NANOmodules/NANO-Minipops/CODE/NANO-Minipops/Includes.h

// All in the spirit of open-source and open-hardware
//
// Minipops rhythm box (c) DSP Synthesizers 2016
// Code by Jan Ostman
// 
// Design by Jorge Gutiérrez
// 
// 2018 Spain
//
// Free for non commercial use
//
// NANO Modules
//
// O2 Minipops rhythm box (c) DSP Synthesizers 2016
// Free for non commercial use

// http://janostman.wordpress.com


// The value will quickly become too large for an int to store
unsigned long previousMicros = 0; 
unsigned long currentMicros = 0;

//--------- Ringbuf parameters ----------
uint8_t Ringbuffer[256];
uint8_t RingWrite=0;
uint8_t RingRead=0;
uint8_t activeRead=5;
volatile uint8_t RingCount=0;
volatile uint16_t SFREQ;
//-----------------------------------------

//Patterns GU BG2 BD CL CW MA CY QU
/*
16 steps
------------
Hard rock
Disco
Reggae
Rock
Samba
Rumba
Cha-Cha
Swing
Bossa Nova
Beguine
Synthpop
12-steps
---------
Boogie
Waltz
Jazz rock
Slow rock
Oxygen
 */

const unsigned char patlen[16] PROGMEM = {15,15,15,15,15,15,15,15,15,15,15,11,11,11,11,11};

const unsigned char pattern[256] PROGMEM = {
B00101100,      //Hard rock16
B00000000,
B00000100,
B00000000,
B00101110,
B00000000,
B00100100,
B00000000,
B00101100,
B00000000,
B00000100,
B00000000,
B00101110,
B00000000,
B00000100,
B00000000,

B00100100,      //Disco16
B00000000,
B00000100,
B00010100,
B00100110,
B00000000,
B00000001,
B00000100,
B00100100,
B00000000,
B00000100,
B00000100,
B01100110,
B00000100,
B01000001,
B00000000,

B01000001,      //Reegae16
B00000100,
B10000000,
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
};
